lucasgomezortiz/RespirAR-DIY/Hardware/Electronica/PCB/REES Kicad/Modelos 3D/LM7805.STEP

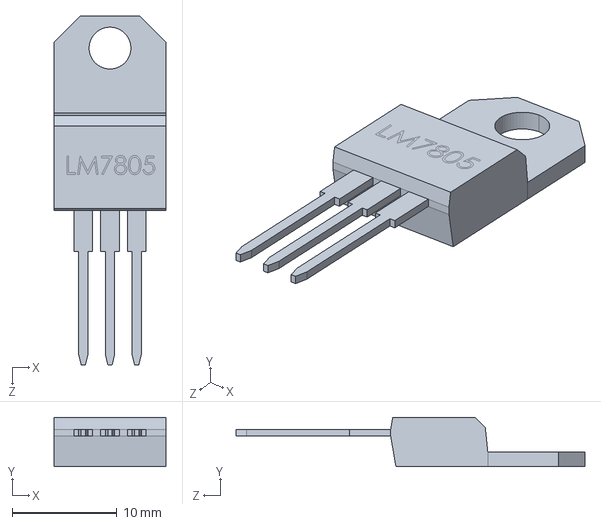
[picture p30: CAD file, 2020-03-21]
Hardware/Electronica/PCB/REES Kicad/Modelos 3D/LM7805.STEP
10.7 x 4.70 x 33.2 mm
