lucasgomezortiz/RespirAR-DIY/Hardware/Respirador/STL/Producion/Ambu_b.stl

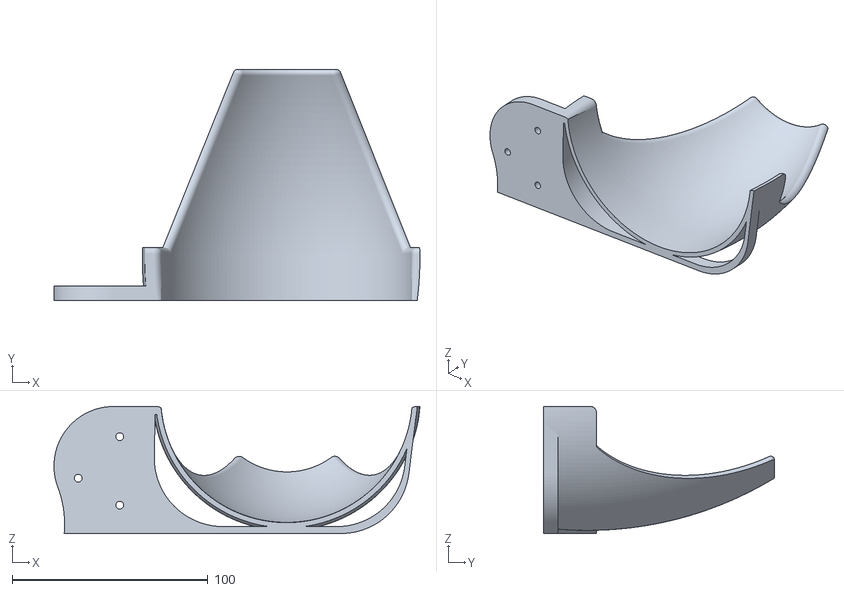
[picture p31: CAD file, 2020-03-21]
Hardware/Respirador/STL/Producion/Ambu_b.stl
187.1 x 118.2 x 64.9
