lucasgomezortiz/RespirAR-DIY/Software/rees_firmware/utils.h

#ifndef UTILS_H
#define UTILS_H

// =========================================================================
// FUNCIONES DE CÁLCULO
// =========================================================================

/**
 * @brief estima el volumen tidal en función de estatura y sexo, en ml.
 *
 * @param estatura en cm, del paciente
 * @param sexo 0: varón, 1: mujer, sexo del paciente
 * @return *volumenTidal volumen tidal estimado, en mililitros
 */
void calcularVolumenTidal(int* volumenTidal, int estatura, int sexo) {
  float peso0, pesoIdeal, volumenEstimado;
  if (sexo == 0) { // Varón
    peso0 = 50.0;
  } else if (sexo == 1) { // Mujer
    peso0 = 45.5;
  }
  pesoIdeal = peso0 + 0.91 * (estatura - 152.4); // en kg

  *volumenTidal = int(round(pesoIdeal * DEFAULT_ML_POR_KG_DE_PESO_IDEAL));
}

/**
 * @brief calcula los tiempos de ciclo, inspiratorio y espiratorio, en seg.
 *
 * Calcula a partir de las respiraciones por minuto, los tiempos de ciclo,
 * inspiratorio y espiratorio, y las velocidades uno y dos.
 * @param speedIns TODO: explicación?
 * @param speedEsp TODO: explicación?
 * @param tIns tiempo de inspiracion, en segundos
 * @param tEsp tiempo de espiracion, en segundos
 * @param tCiclo tiempo de ciclo, en segundos
 * @param pasosPorRevolucion TODO: explicación?
 * @param microStepper TODO: explicación?
 * @param porcentajeInspiratorio fraccion del ciclo en la que se inspira, tIns/tCiclo*100
 * @param rpm respiraciones por minuto
 */
void calcularCicloInspiratorio(float* speedIns, float* speedEsp,
                               float* tIns, float* tEsp, float* tCiclo,
                               int pasosPorRevolucion, int microStepper,
                               int porcentajeInspiratorio, int rpm) {
  *tCiclo = 60 / rpm; // Tiempo de ciclo en segundos
  *tIns = *tCiclo * porcentajeInspiratorio/100;
  *tEsp = *tCiclo - *tIns;

  *speedIns = (pasosPorRevolucion * microStepper / 2) / *tIns; // TODO: unidades?
  *speedEsp = (pasosPorRevolucion * microStepper / 2) / *tEsp; // TODO: unidades?
}

#endif // UTILS_H
